ArqueologiaDigital/PatinhoFeio_KICAD/CT3-6/CT3-6.pdf

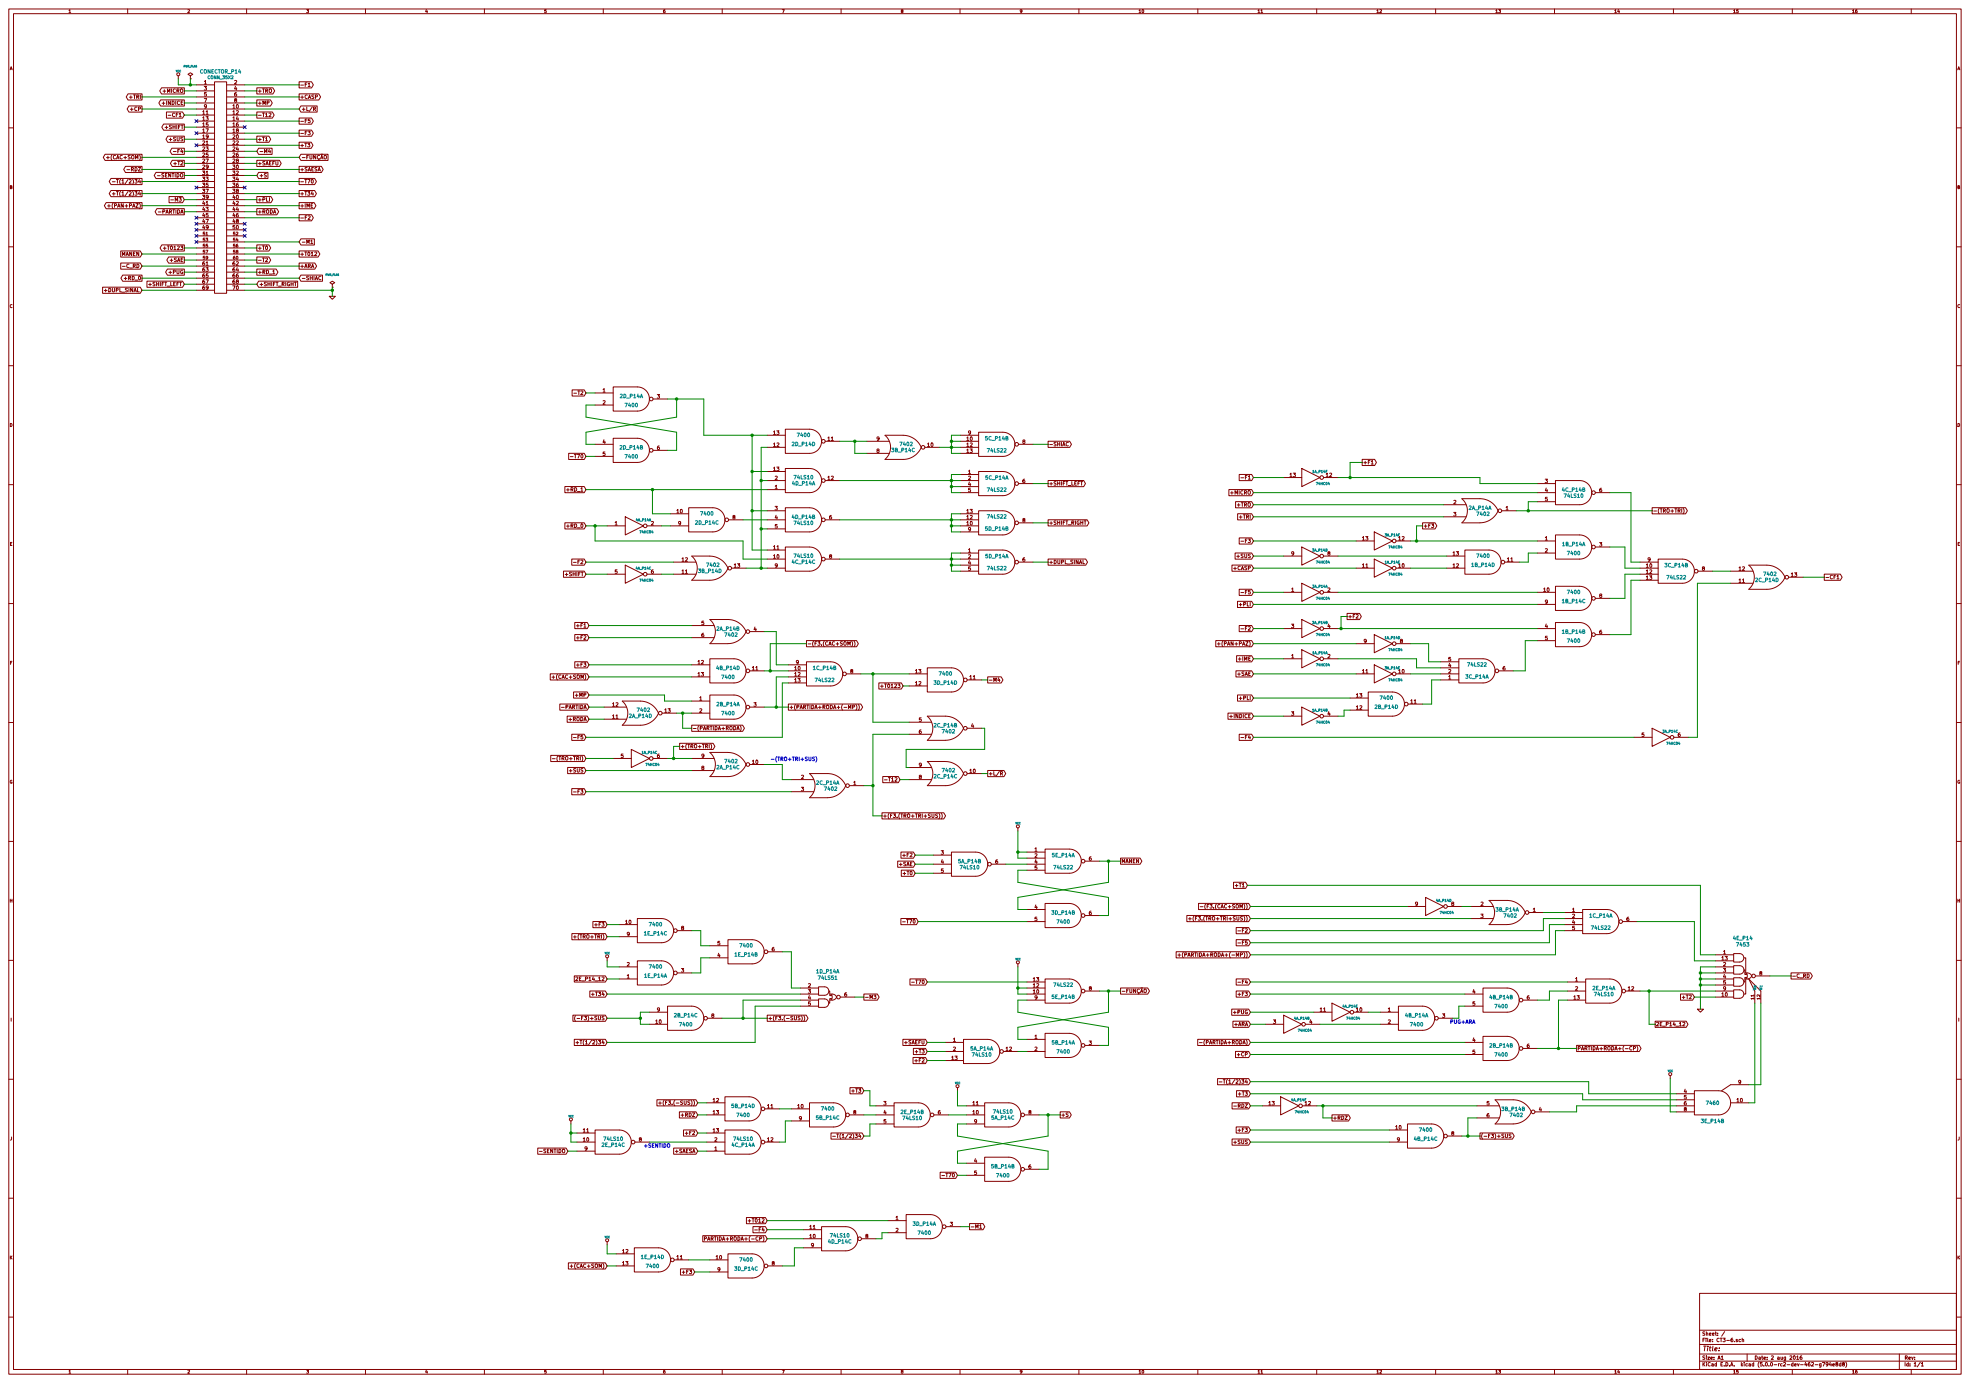
[picture p34: page 1]

Id: 1/1 Title: File: CT3-6.sch Sheet: /
