ArqueologiaDigital/PatinhoFeio_KICAD/CT2-5/CT2-5.pdf

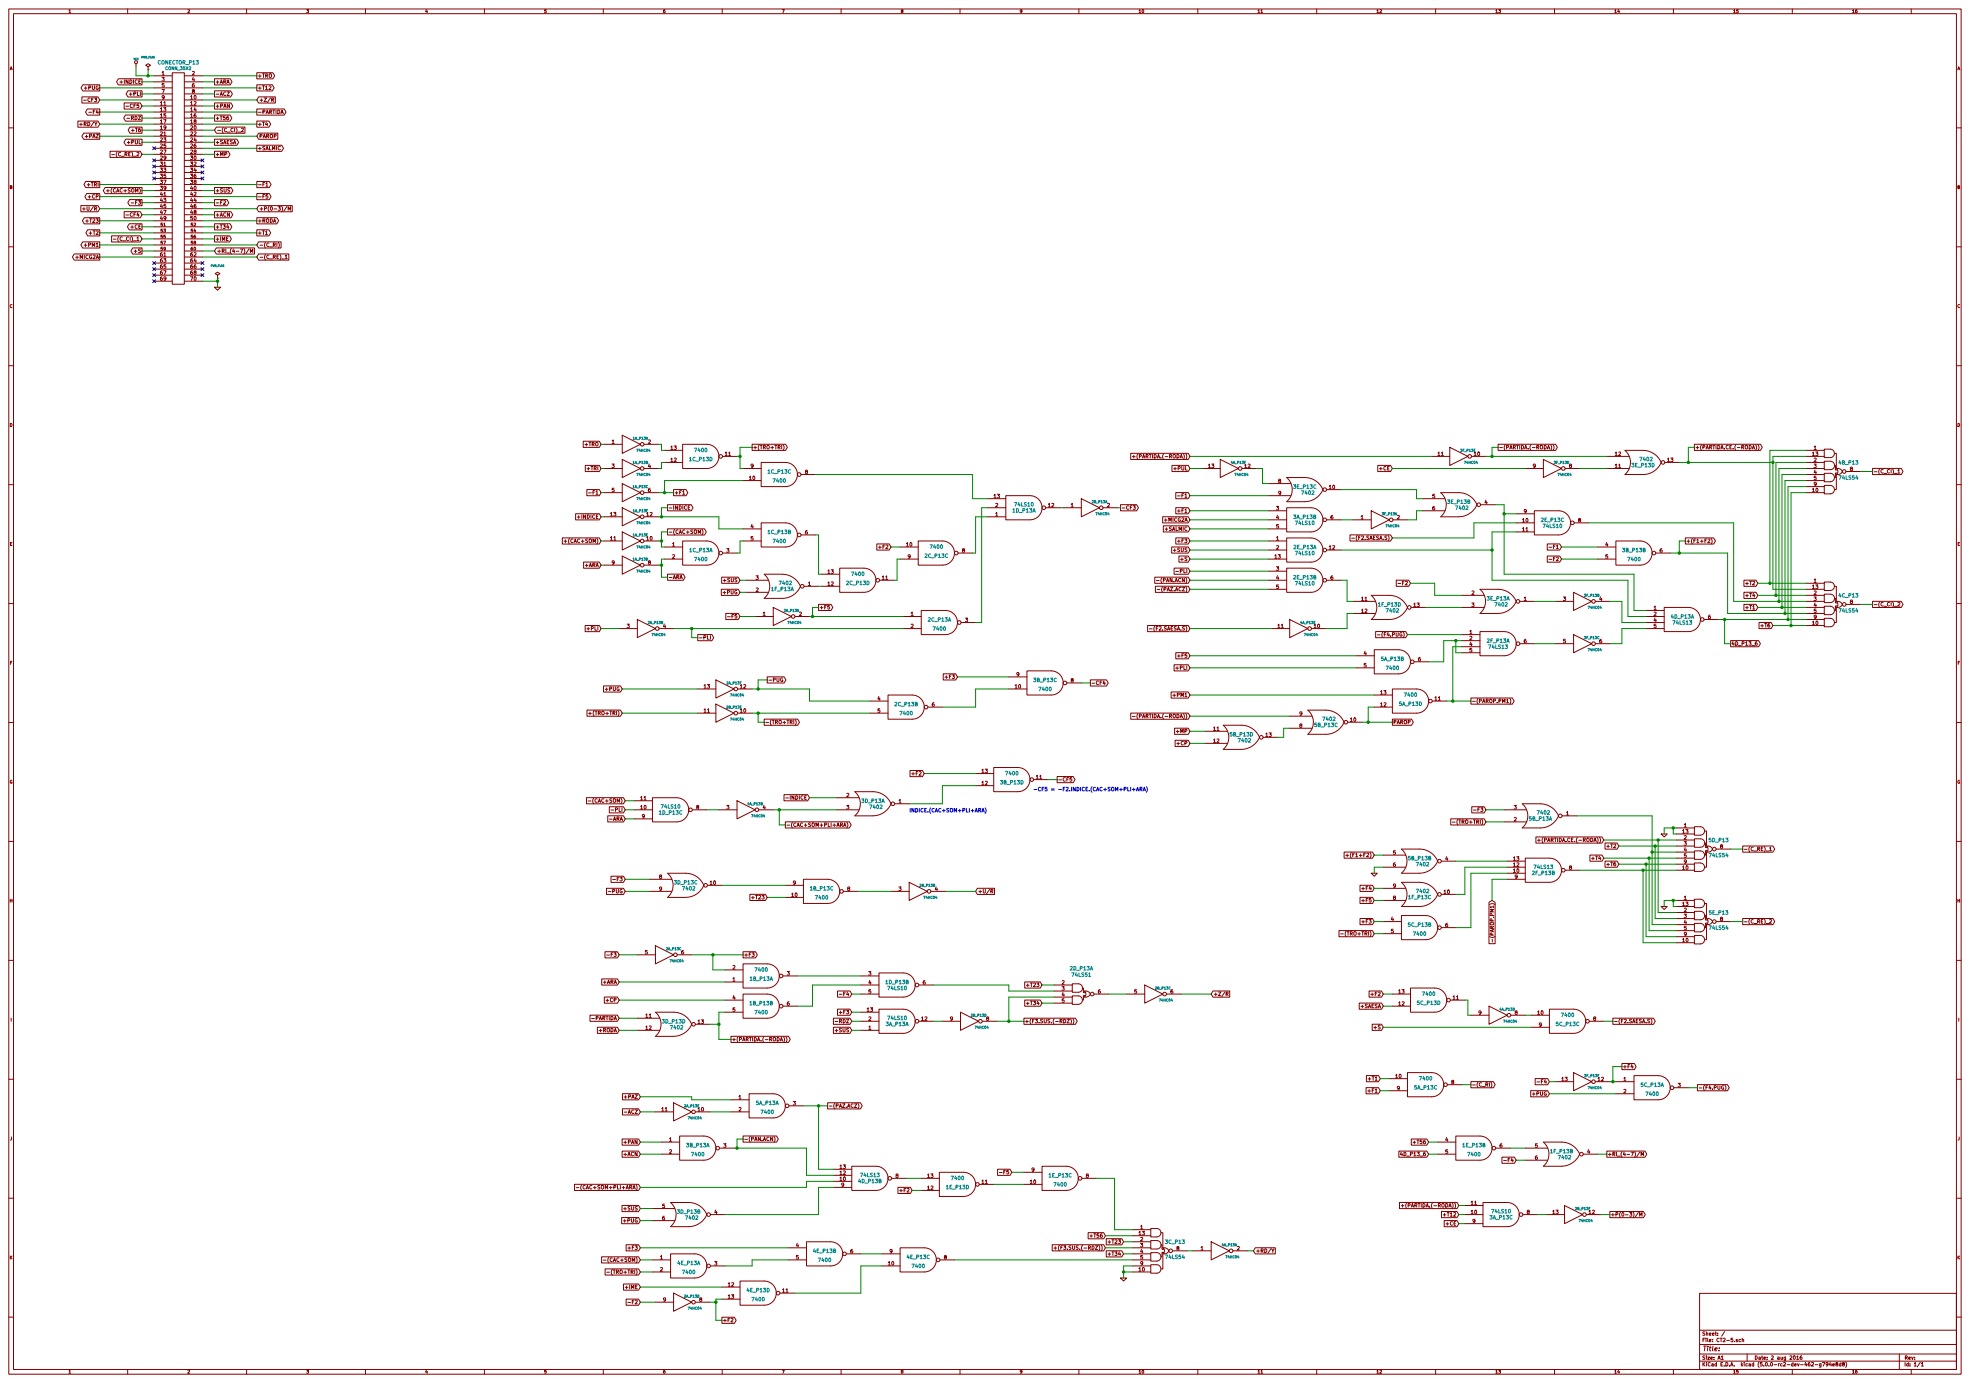
[picture p35: page 1]

-CF5 = -F2.INDICE.(CAC+SOM+PLI+ARA) 10

INDICE.(CAC+SOM+PLI+ARA)

-(CAC+SOM+PLI+ARA)

-(CAC+SOM+PLI+ARA) +PAN

Id: 1/1 Title: File: CT2-5.sch Sheet: /
