ArqueologiaDigital/PatinhoFeio_KICAD/CT1-4/CT1-4.pdf

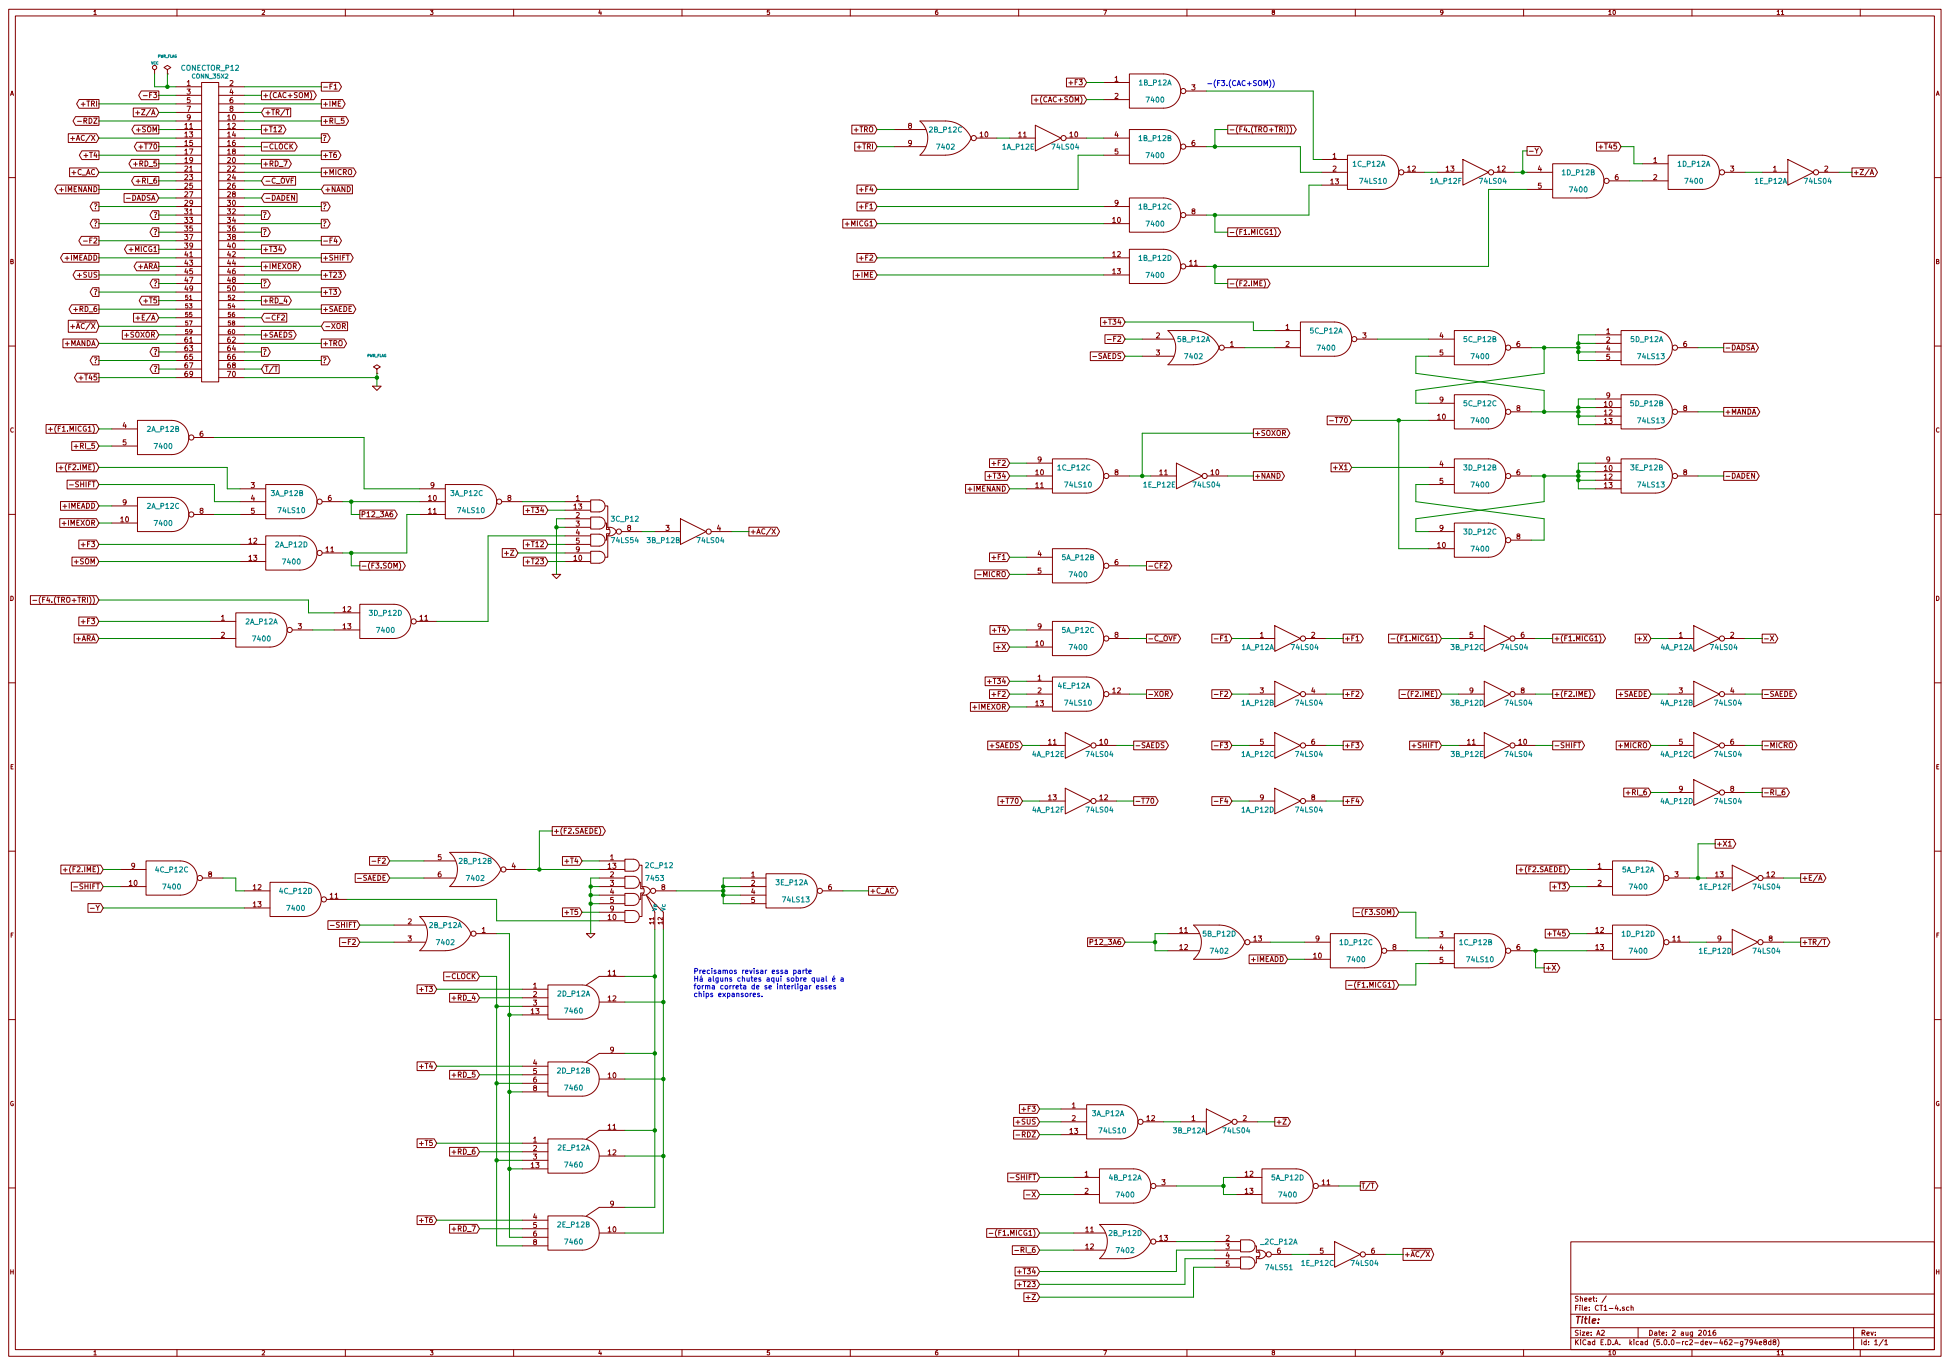
[picture p36: page 1]

Há alguns chutes aqui sobre qual é a
forma correta de se interligar esses
chips expansores.

13

Id: 1/1 Title: File: CT1-4.sch Sheet: /
