ArqueologiaDigital/PatinhoFeio_KICAD/CDE-3/CDE-3.pdf

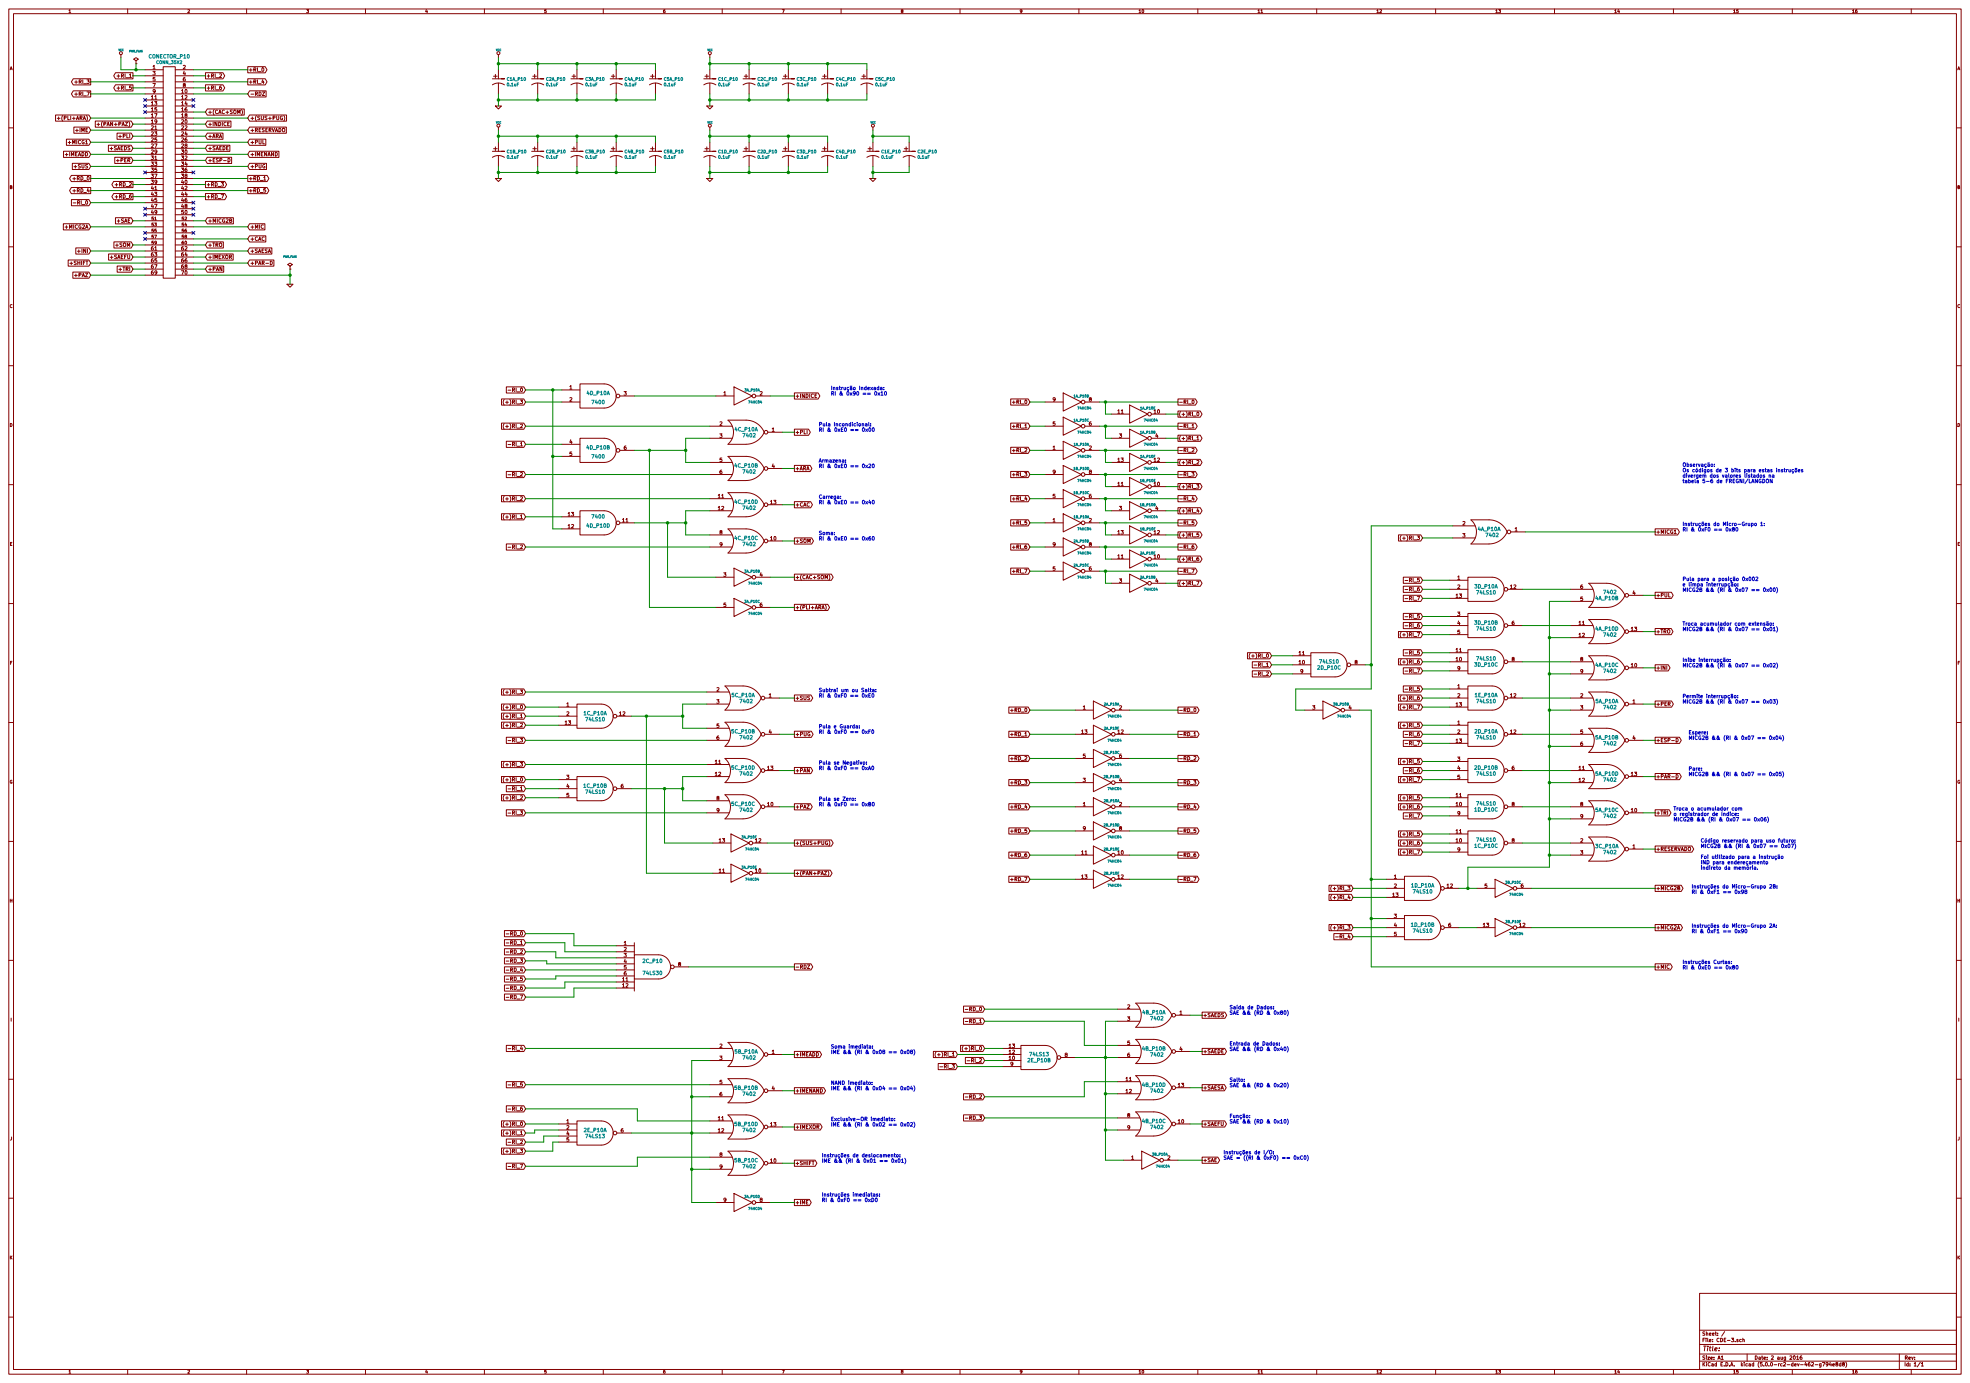
[picture p37: page 1]

Pula Incondicional: RI & 0xE0 == 0x00 Armazena: RI & 0xE0 == 0x20 Carrega: RI & 0xE0 == 0x40 Soma: RI & 0xE0 == 0x60 1 23

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

Instruções do Micro-Grupo 1: RI & 0xF0 == 0x80

Pula para a posição 0x002
e limpa interrupção:
MICG2B && (RI & 0x07 == 0x00) Troca acumulador com extensão: MICG2B && (RI & 0x07 == 0x01)
+PUL +TRO

Subtrai um ou Salta: RI & 0xF0 == 0xE0 Pula e Guarda: RI & 0xF0 == 0xF0 Pula se Negativo: RI & 0xF0 == 0xA0 Pula se Zero: RI & 0xF0 == 0xB0

Espere:
MICG2B && (RI & 0x07 == 0x04) Pare: MICG2B && (RI & 0x07 == 0x05) Troca o acumulador com

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

Instruções do Micro-Grupo 2B: RI & 0xF1 == 0x98

Instruções do Micro-Grupo 2A: RI & 0xF1 == 0x90

Id: 1/1 Title: File: CDE-3.sch Sheet: / 1 23

SAE && (RD & 0x20) Entrada de Dados: SAE && (RD & 0x40)

Soma imediata:
IME && (RI & 0x08 == 0x08) NAND imediato:
