ArqueologiaDigital/PatinhoFeio_KICAD/CCE-2/CCE-2.pdf

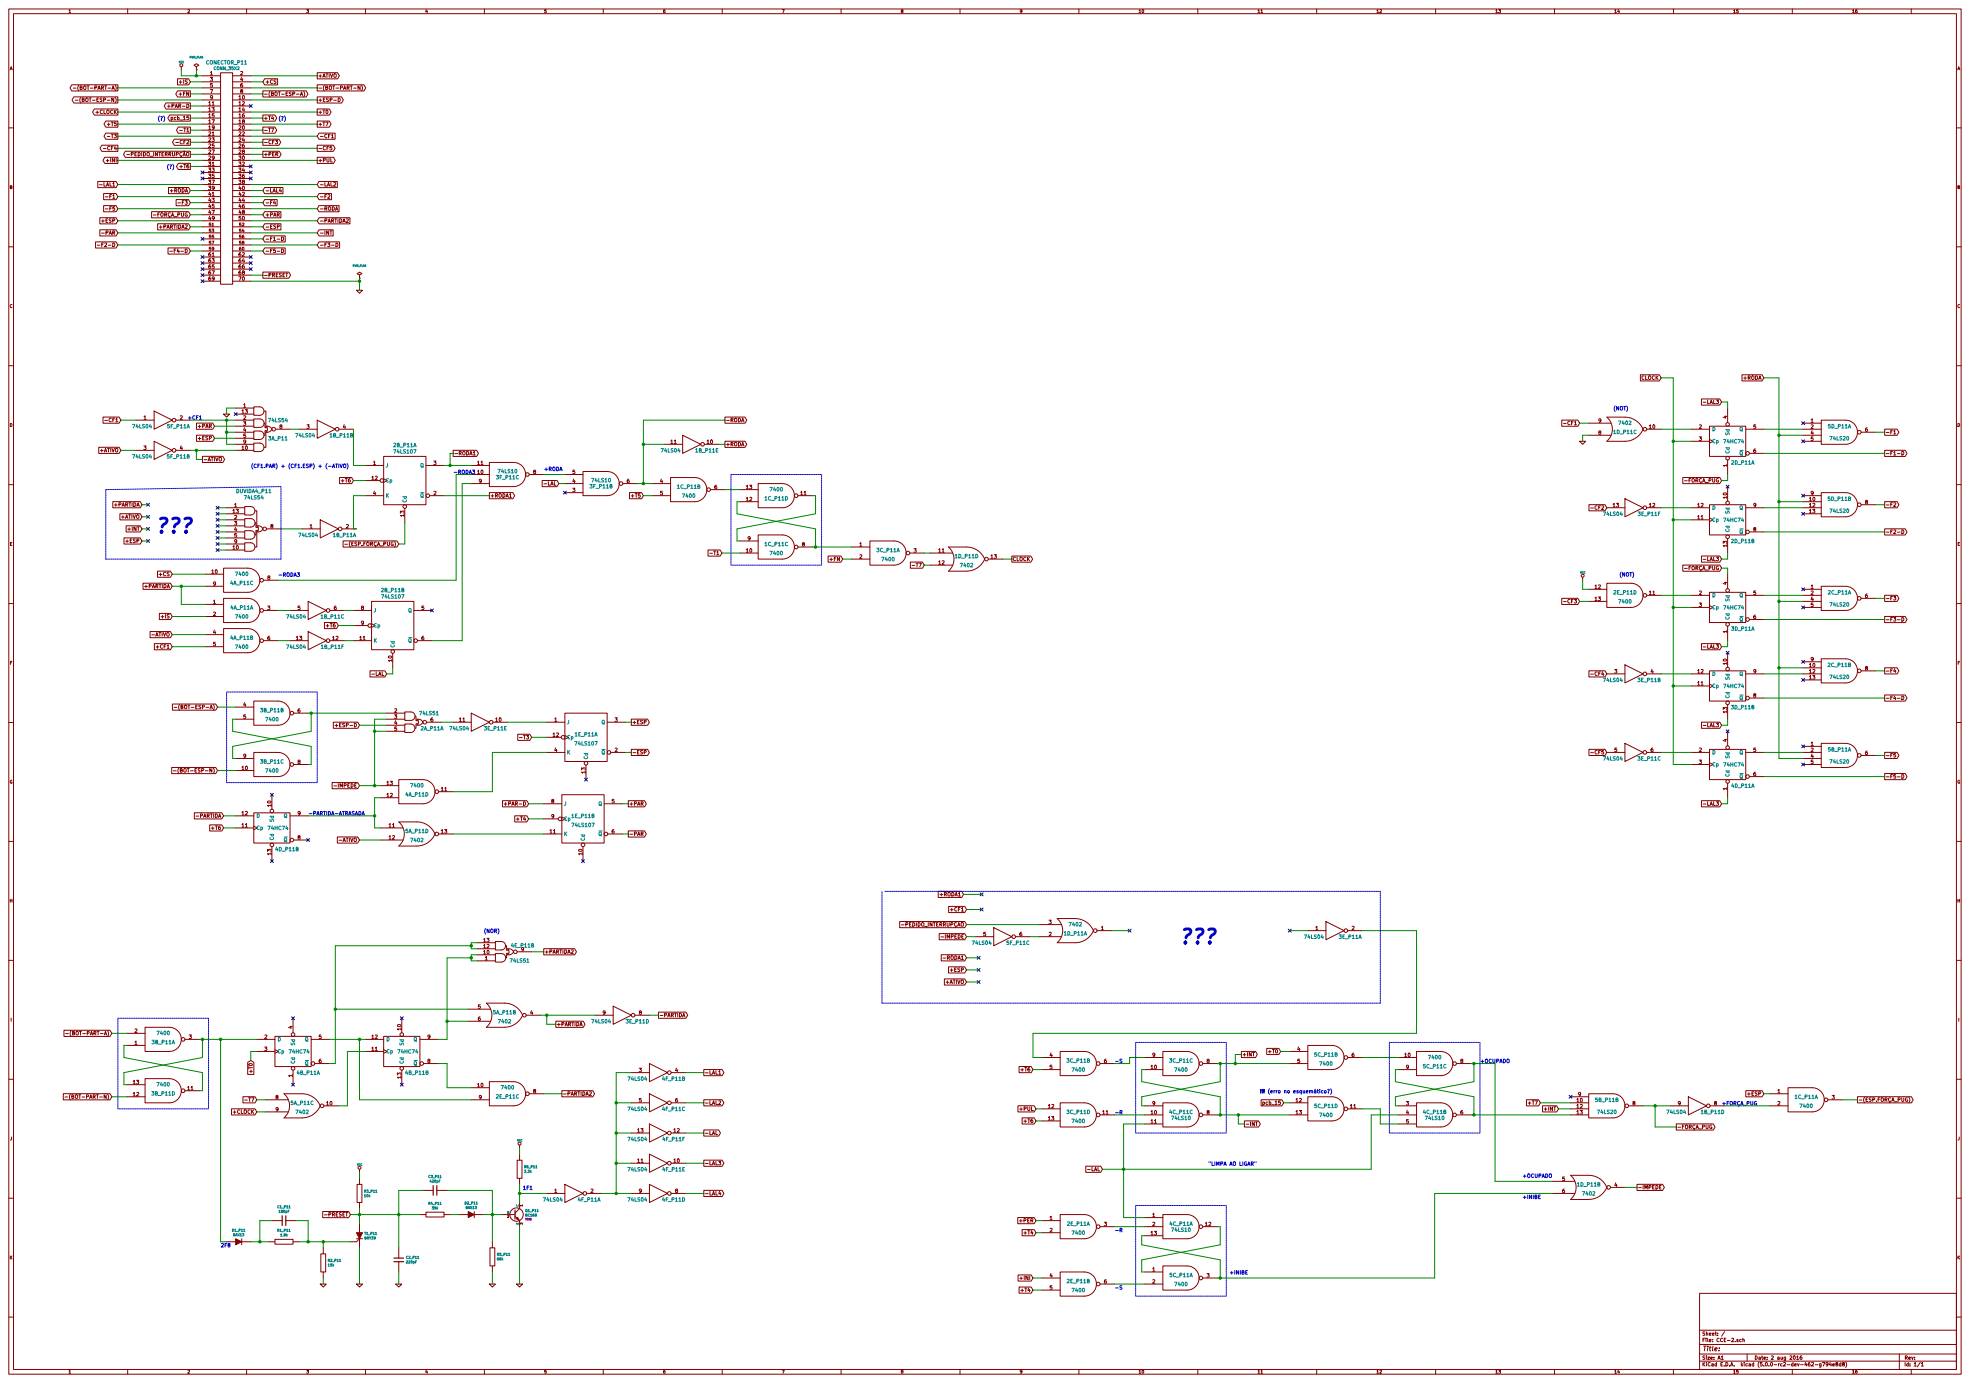
[picture p38: page 1]

Id: 1/1 Title: File: CCE-2.sch Sheet: /
