ArqueologiaDigital/PatinhoFeio_KICAD/CRC-1/CRC-1.pdf

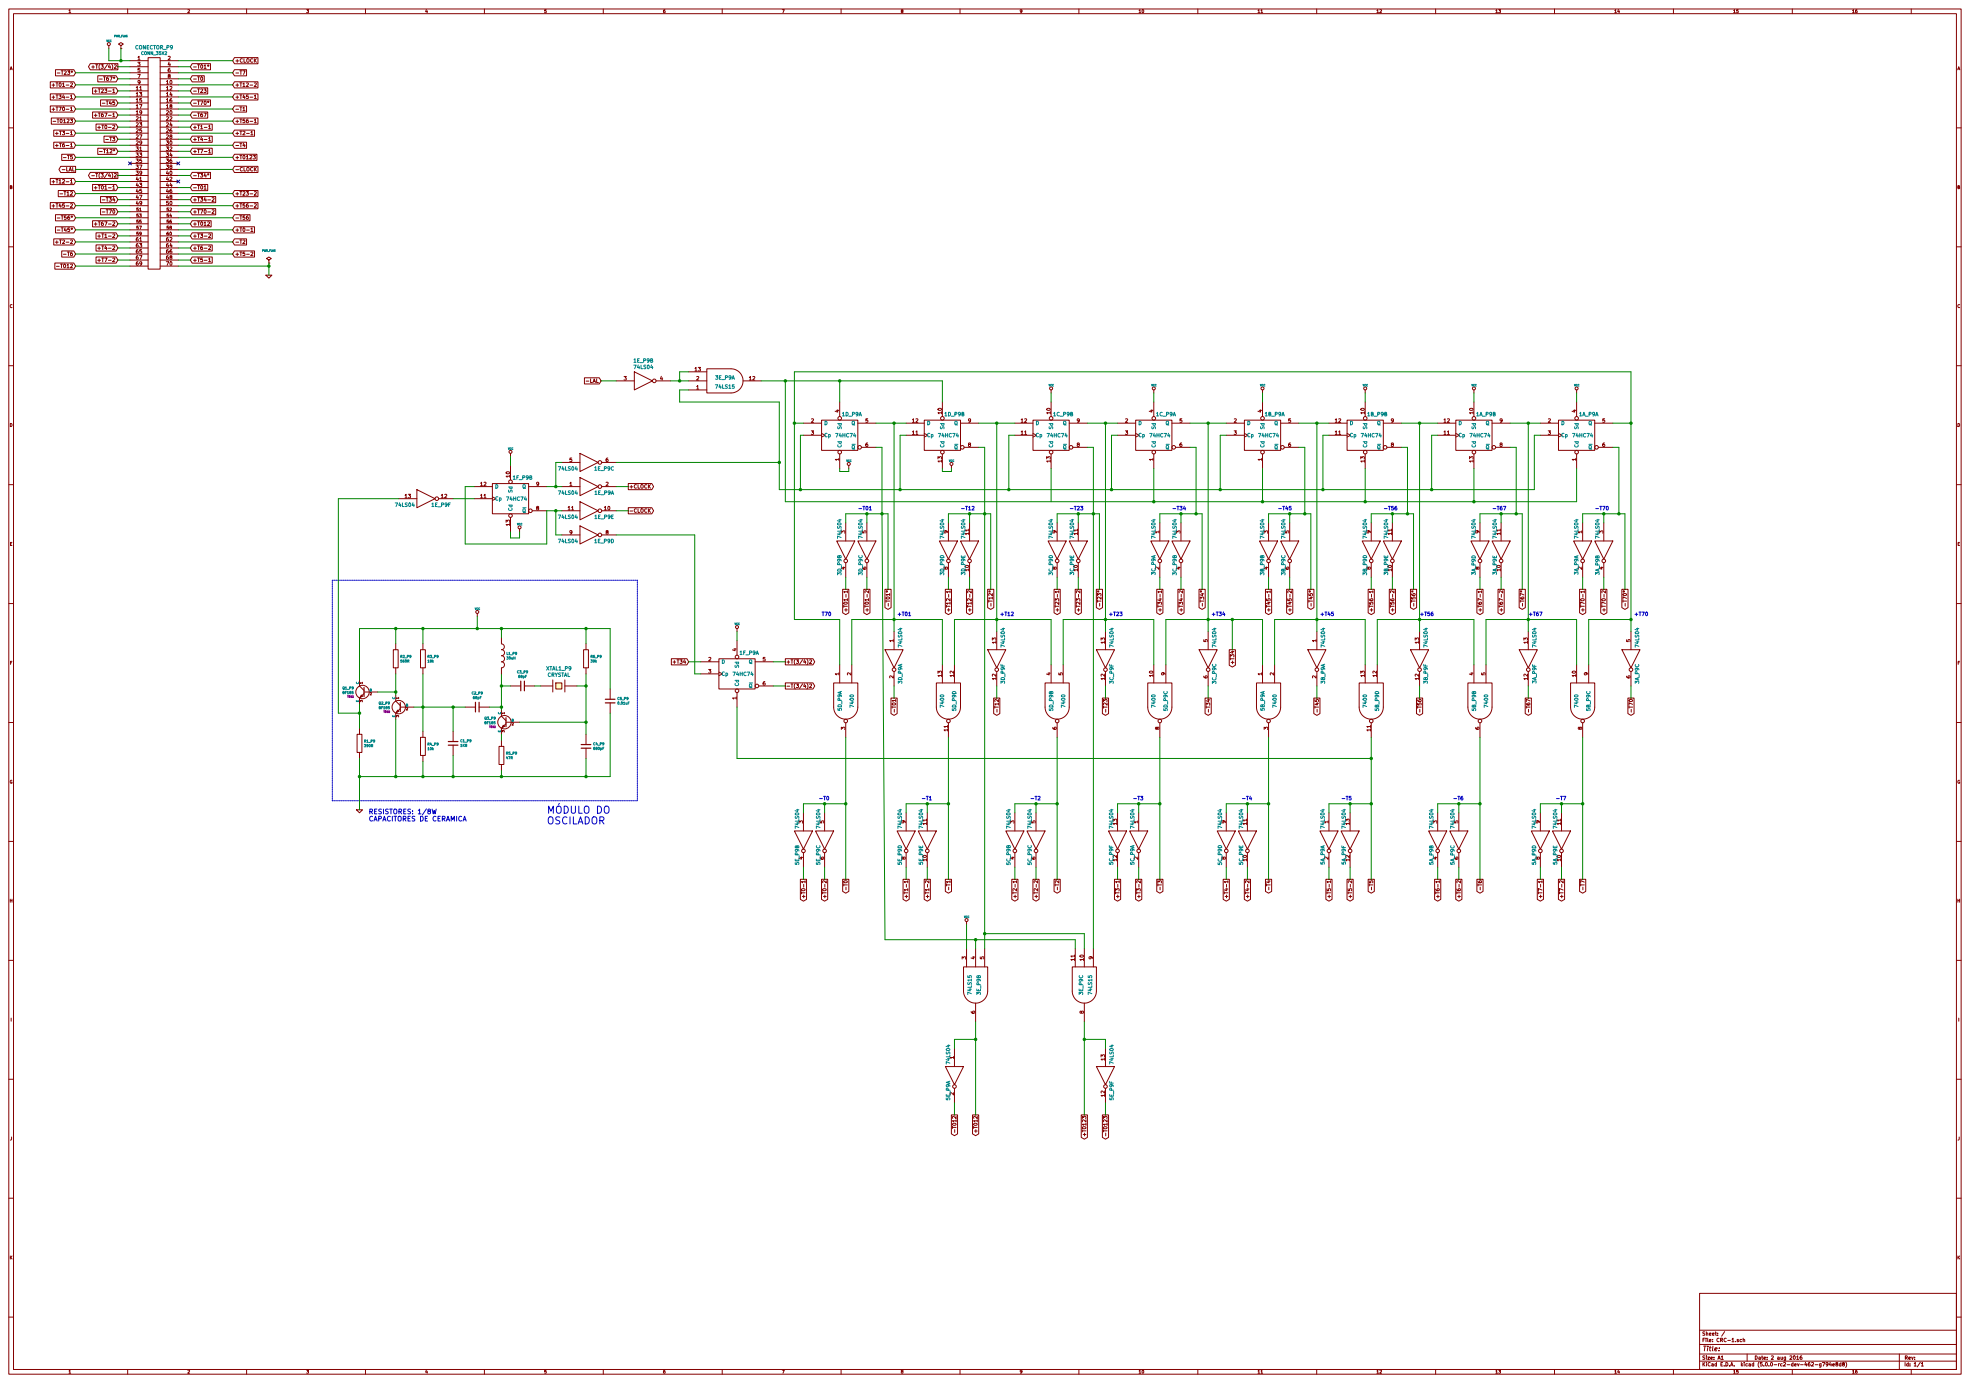
[picture p39: page 1]

Id: 1/1 Title: File: CRC-1.sch Sheet: /
