ArqueologiaDigital/PatinhoFeio_KICAD/CDE-3/CDE-3.cir

.title KiCad schematic
44B_P10 +SAEDS -RD_0 Net-_2E_P10-Pad8_ +SAEDE -RD_1 Net-_2E_P10-Pad8_ GND -RD_3 Net-_2E_P10-Pad8_ +SAEFU -RD_2 Net-_2E_P10-Pad8_ +SAESA VCC 7402
33B_P10 Net-_2E_P10-Pad8_ +SAE Net-_2D_P10-Pad8_ +MIC Net-_1D_P10-Pad12_ +MICG2B GND +MICG2A Net-_1D_P10-Pad6_ VCC 74HC04
22E_P10 _+_RI_0 _+_RI_1 -RI_2 _+_RI_3 Net-_2E_P10-Pad6_ GND Net-_2E_P10-Pad8_ -RI_3 -RI_2 _+_RI_1 _+_RI_0 VCC 74LS13
22B_P10 +RD_4 -RD_4 +RD_3 -RD_3 +RD_2 -RD_2 GND -RD_5 +RD_5 -RD_6 +RD_6 -RD_7 +RD_7 VCC 74HC04
22A_P10 +RD_0 -RD_0 -RI_7 _+_RI_7 +RI_7 -RI_7 GND -RI_6 +RI_6 _+_RI_6 -RI_6 -RD_1 +RD_1 VCC 74HC04
11B_P10 +RI_5 -RI_5 -RI_4 _+_RI_4 +RI_4 -RI_4 GND -RI_3 +RI_3 _+_RI_3 -RI_3 _+_RI_5 -RI_5 VCC 74HC04
11A_P10 +RI_2 -RI_2 -RI_1 _+_RI_1 +RI_1 -RI_1 GND -RI_0 +RI_0 _+_RI_0 -RI_0 _+_RI_2 -RI_2 VCC 74HC04
44C_P10 +PLI _+_RI_2 Net-_3A_P10-Pad5_ +ARA Net-_3A_P10-Pad5_ -RI_2 GND Net-_3A_P10-Pad3_ -RI_2 +SOM _+_RI_2 Net-_3A_P10-Pad3_ +CAC VCC 7402
33A_P10 Net-_3A_P10-Pad1_ +INDICE Net-_3A_P10-Pad3_ +_CAC+SOM_ Net-_3A_P10-Pad5_ +_PLI+ARA_ GND +IME Net-_2E_P10-Pad6_ +_PAN+PAZ_ Net-_1C_P10-Pad12_ +_SUS+PUG_ Net-_1C_P10-Pad6_ VCC 74HC04
44D_P10 -RI_0 _+_RI_3 Net-_3A_P10-Pad1_ -RI_1 -RI_0 Net-_3A_P10-Pad5_ GND Net-_3A_P10-Pad3_ -RI_0 _+_RI_1 VCC 7400
55C_P10 +SUS _+_RI_3 Net-_1C_P10-Pad12_ +PUG Net-_1C_P10-Pad12_ -RI_3 GND Net-_1C_P10-Pad6_ -RI_3 +PAZ _+_RI_3 Net-_1C_P10-Pad6_ +PAN VCC 7402
11C_P10 _+_RI_0 _+_RI_1 _+_RI_0 -RI_1 _+_RI_2 Net-_1C_P10-Pad6_ GND Net-_1C_P10-Pad8_ _+_RI_7 _+_RI_6 _+_RI_5 Net-_1C_P10-Pad12_ _+_RI_2 VCC 74LS10
55B_P10 +IMEADD -RI_4 Net-_2E_P10-Pad6_ +IMENAND -RI_5 Net-_2E_P10-Pad6_ GND -RI_7 Net-_2E_P10-Pad6_ +SHIFT -RI_6 Net-_2E_P10-Pad6_ +IMEXOR VCC 7402
55A_P10 +PER Net-_1E_P10-Pad12_ Net-_1D_P10-Pad12_ +ESP-D Net-_2D_P10-Pad12_ Net-_1D_P10-Pad12_ GND Net-_1D_P10-Pad8_ Net-_1D_P10-Pad12_ +TRI Net-_2D_P10-Pad6_ Net-_1D_P10-Pad12_ +PAR-D VCC 7402
33C_P10 +RESERVADO Net-_1C_P10-Pad8_ Net-_1D_P10-Pad12_ GND VCC 7402
44A_P10 +MICG1 Net-_2D_P10-Pad8_ _+_RI_3 +PUL Net-_1D_P10-Pad12_ Net-_3D_P10-Pad12_ GND Net-_3D_P10-Pad8_ Net-_1D_P10-Pad12_ +INI Net-_3D_P10-Pad6_ Net-_1D_P10-Pad12_ +TRO VCC 7402
33D_P10 -RI_5 -RI_6 -RI_5 -RI_6 _+_RI_7 Net-_3D_P10-Pad6_ GND Net-_3D_P10-Pad8_ -RI_7 _+_RI_6 -RI_5 Net-_3D_P10-Pad12_ -RI_7 VCC 74LS10
11E_P10 -RI_5 _+_RI_6 GND Net-_1E_P10-Pad12_ _+_RI_7 VCC 74LS10
22D_P10 _+_RI_5 -RI_6 _+_RI_5 -RI_6 _+_RI_7 Net-_2D_P10-Pad6_ GND Net-_2D_P10-Pad8_ -RI_2 -RI_1 _+_RI_0 Net-_2D_P10-Pad12_ -RI_7 VCC 74LS10
11D_P10 +MIC _+_RI_3 +MIC _+_RI_3 -RI_4 Net-_1D_P10-Pad6_ GND Net-_1D_P10-Pad8_ -RI_7 _+_RI_6 _+_RI_5 Net-_1D_P10-Pad12_ _+_RI_4 VCC 74LS10
22C_P10 -RD_0 -RD_1 -RD_2 -RD_3 -RD_4 -RD_5 GND -RDZ -RD_6 -RD_7 VCC 74LS30
CCONECTOR_P10 VCC +RI_0 +RI_1 +RI_2 +RI_3 +RI_4 +RI_5 +RI_6 +RI_7 -RDZ ? ? ? ? ? +_CAC+SOM_ +_PLI+ARA_ +_SUS+PUG_ +_PAN+PAZ_ +INDICE +IME +RESERVADO +PLI +ARA +MICG1 +PUL +SAEDS +SAEDE +IMEADD +IMENAND +PER +ESP-D +SUS +PUG ? ? +RD_0 +RD_1 +RD_2 +RD_3 +RD_4 +RD_5 +RD_6 +RD_7 -RI_0 ? ? ? ? ? +SAE +MICG2B +MICG2A +MIC ? ? ? +CAC +SOM +TRO +INI +SAESA +SAEFU +IMEXOR +SHIFT +PAR-D +TRI +PAN +PAZ GND CONN_35X2
.end
